AziDesigns/IRLKTANE/IRLKTANE/knob.h

// On the Subject of Knobs
/*
  KNOWN ISSUES:
  MODULE FULLY FUNCTIONS FROM A LED RANDOMAZATION, KNOB TRACKING, AND RESETTING TIME ETC,
    HOWEVER THE UP POSITION HAS STILL NOT BEEN DETERMINED, IN GAME UP IS ROTATED TO BE LEFT RIGHT UP OR DOWN AT RANDOM EACH TIME IT RESETS. 
    MINE IS CURRENTLY GOING TO BE HARD VALUE OF UP = UP AND NO MOVING LABEL. MAY ADD A MOTOR THAT ROTATES THE UP POSITION IN THE FUTURE.
*/
#define KNOB_DEFAULT_TIME 40 // default time per rotation
#define PIN_KNOB_ROTARY_SWITCH A0 // rotary switch analog input pin
#define PIN_KNOB_LED_1  2,1,1
#define PIN_KNOB_LED_2  2,2,1
#define PIN_KNOB_LED_3  2,3,1
#define PIN_KNOB_LED_4  2,4,1
#define PIN_KNOB_LED_5  2,5,1
#define PIN_KNOB_LED_6  2,6,1l
#define PIN_KNOB_LED_7  2,7,1
#define PIN_KNOB_LED_8  2,0,2
#define PIN_KNOB_LED_9  2,1,2
#define PIN_KNOB_LED_10 2,2,2
#define PIN_KNOB_LED_11 2,3,2
#define PIN_KNOB_LED_12 2,4,2
#define KNOB_POSITION_4 200
#define KNOB_POSITION_3 300
#define KNOB_POSITION_2 450
#define KNOB_POSITION_1 1023

unsigned long knobSeconds = 0;
byte knobSec = KNOB_DEFAULT_TIME + 1;

byte knobLEDArray = 0;
int knobPositionValue = 0;
byte knobCurrentState = 0;
byte knobCorrectState = 0;

void knobSetup() 
{
  if (DEBUG_LEVEL >= 3) {
    Serial.println (__func__);
  }
  knobLEDArray = random(8);
};

void knobCheckKnobPosition() // function that checks if the knob is in the correct position when it hits -1
{
  knobPositionValue = analogRead(PIN_KNOB_ROTARY_SWITCH); // uncomment once the knob is wired up. Right now its not wired at all.
  if (knobPositionValue<=KNOB_POSITION_4){
    if (DEBUG_LEVEL >= 1) {
      Serial.println(F("Position 4"));
    }
    knobCurrentState = 4;
  } else if (knobPositionValue<=KNOB_POSITION_3) {
    if (DEBUG_LEVEL >= 1) {
      Serial.println(F("Position 3"));
    }
    knobCurrentState = 3;
  } else if (knobPositionValue<=KNOB_POSITION_2) {
    if (DEBUG_LEVEL >= 1) {
      Serial.println(F("Position 2"));
    }
    knobCurrentState = 2;
  } else if (knobPositionValue<=KNOB_POSITION_1) {
    if (DEBUG_LEVEL >= 1) {
      Serial.println(F("Position 1"));
    }
    knobCurrentState = 1;
  }
}

void knobDisplayTime() // function that displays the time on the clock
{
  if (DEBUG_LEVEL >= 3) {
    Serial.println (__func__);
  }
  if (knobSeconds < millis()) {
    knobSeconds += 1000;
    knobSec--;
    if (knobSec == -1) {
      knobCheckKnobPosition();
      if (knobCurrentState==knobCorrectState) { 
        knobSec=KNOB_DEFAULT_TIME + 1; // command to restart the countdown timer
        knobLEDArray = random(8); // choses a new random array of LED's to display
      } else {
        addStrike(); // if the time hits zero and the correct knob position is not set the bomb will add a stike
        knobModuleStike = true;
        lc.setDigit(1,5,' ',false);
        lc.setDigit(1,4,' ',false); 
        lc.setLed(PIN_KNOB_LED_1,false);
        lc.setLed(PIN_KNOB_LED_2,false);
        lc.setLed(PIN_KNOB_LED_3,false);
        lc.setLed(PIN_KNOB_LED_4,false);
        lc.setLed(PIN_KNOB_LED_5,false);
        lc.setLed(PIN_KNOB_LED_6,false);
        lc.setLed(PIN_KNOB_LED_7,false);
        lc.setLed(PIN_KNOB_LED_8,false);
        lc.setLed(PIN_KNOB_LED_9,false);
        lc.setLed(PIN_KNOB_LED_10,false);
        lc.setLed(PIN_KNOB_LED_11,false);
        lc.setLed(PIN_KNOB_LED_12,false);
      }
    }
    needyDigitDisplay(1, 4, 5, knobSec);
  }
}

void knobDisplayLEDArray()
{
  if (knobLEDArray==0) {
    knobCorrectState=0; // correct position = up
    lc.setLed(PIN_KNOB_LED_1,false);
    lc.setLed(PIN_KNOB_LED_2,false);
    lc.setLed(PIN_KNOB_LED_3,true);
    lc.setLed(PIN_KNOB_LED_4,false);
    lc.setLed(PIN_KNOB_LED_5,true);
    lc.setLed(PIN_KNOB_LED_6,true);
    lc.setLed(PIN_KNOB_LED_7,true);
    lc.setLed(PIN_KNOB_LED_8,true);
    lc.setLed(PIN_KNOB_LED_9,true);
    lc.setLed(PIN_KNOB_LED_10,true);
    lc.setLed(PIN_KNOB_LED_11,false);
    lc.setLed(PIN_KNOB_LED_12,true);
  } else if (knobLEDArray==1) {
    knobCorrectState=0; // correct position = up
    lc.setLed(PIN_KNOB_LED_1,true);
    lc.setLed(PIN_KNOB_LED_2,false);
    lc.setLed(PIN_KNOB_LED_3,true);
    lc.setLed(PIN_KNOB_LED_4,false);
    lc.setLed(PIN_KNOB_LED_5,true);
    lc.setLed(PIN_KNOB_LED_6,false);
    lc.setLed(PIN_KNOB_LED_7,false);
    lc.setLed(PIN_KNOB_LED_8,true);
    lc.setLed(PIN_KNOB_LED_9,true);
    lc.setLed(PIN_KNOB_LED_10,false);
    lc.setLed(PIN_KNOB_LED_11,true);
    lc.setLed(PIN_KNOB_LED_12,true);
  } else if (knobLEDArray==2) {
    knobCorrectState=2; // correct position = down
    lc.setLed(PIN_KNOB_LED_1,false);
    lc.setLed(PIN_KNOB_LED_2,true);
    lc.setLed(PIN_KNOB_LED_3,true);
    lc.setLed(PIN_KNOB_LED_4,false);
    lc.setLed(PIN_KNOB_LED_5,false);
    lc.setLed(PIN_KNOB_LED_6,true);
    lc.setLed(PIN_KNOB_LED_7,true);
    lc.setLed(PIN_KNOB_LED_8,true);
    lc.setLed(PIN_KNOB_LED_9,true);
    lc.setLed(PIN_KNOB_LED_10,true);
    lc.setLed(PIN_KNOB_LED_11,false);
    lc.setLed(PIN_KNOB_LED_12,true);
  } else if (knobLEDArray==3) {
    knobCorrectState=2; // correct position = down
    lc.setLed(PIN_KNOB_LED_1,true);
    lc.setLed(PIN_KNOB_LED_2,false);
    lc.setLed(PIN_KNOB_LED_3,true);
    lc.setLed(PIN_KNOB_LED_4,false);
    lc.setLed(PIN_KNOB_LED_5,true);
    lc.setLed(PIN_KNOB_LED_6,false);
    lc.setLed(PIN_KNOB_LED_7,false);
    lc.setLed(PIN_KNOB_LED_8,true);
    lc.setLed(PIN_KNOB_LED_9,false);
    lc.setLed(PIN_KNOB_LED_10,false);
    lc.setLed(PIN_KNOB_LED_11,false);
    lc.setLed(PIN_KNOB_LED_12,true);
  } else if (knobLEDArray==4) {
    knobCorrectState=3; // correct position = left
    lc.setLed(PIN_KNOB_LED_1,false);
    lc.setLed(PIN_KNOB_LED_2,false);
    lc.setLed(PIN_KNOB_LED_3,false);
    lc.setLed(PIN_KNOB_LED_4,false);
    lc.setLed(PIN_KNOB_LED_5,true);
    lc.setLed(PIN_KNOB_LED_6,false);
    lc.setLed(PIN_KNOB_LED_7,true);
    lc.setLed(PIN_KNOB_LED_8,false);
    lc.setLed(PIN_KNOB_LED_9,false);
    lc.setLed(PIN_KNOB_LED_10,true);
    lc.setLed(PIN_KNOB_LED_11,true);
    lc.setLed(PIN_KNOB_LED_12,true);
  } else if (knobLEDArray==5) {
    knobCorrectState=3; // correct position = left
    lc.setLed(PIN_KNOB_LED_1,false);
    lc.setLed(PIN_KNOB_LED_2,false);
    lc.setLed(PIN_KNOB_LED_3,false);
    lc.setLed(PIN_KNOB_LED_4,false);
    lc.setLed(PIN_KNOB_LED_5,true);
    lc.setLed(PIN_KNOB_LED_6,false);
    lc.setLed(PIN_KNOB_LED_7,false);
    lc.setLed(PIN_KNOB_LED_8,false);
    lc.setLed(PIN_KNOB_LED_9,false);
    lc.setLed(PIN_KNOB_LED_10,true);
    lc.setLed(PIN_KNOB_LED_11,true);
    lc.setLed(PIN_KNOB_LED_12,false);
  } else if (knobLEDArray==6) {
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
  lc.setLed(PIN_KNOB_LED_5,false);
  lc.setLed(PIN_KNOB_LED_6,false);
  lc.setLed(PIN_KNOB_LED_7,false);
  lc.setLed(PIN_KNOB_LED_8,false);
  lc.setLed(PIN_KNOB_LED_9,false);
  lc.setLed(PIN_KNOB_LED_10,false);
  lc.setLed(PIN_KNOB_LED_11,false);
  lc.setLed(PIN_KNOB_LED_12,false);
}
