AziDesigns/IRLKTANE/IRLKTANE/batteries.h

/*************************************************
   Default values for batteries
 *************************************************/
/*
  KNOWN ISSUES:
  Will eventually become a random number of batteries and actualy display them. For now it is fixed values
*/
byte nrBatteries = 0; // number of batteries // will eventually point to a .h file that controls which batteries are shown
