AziDesigns/IRLKTANE/IRLKTANE/indicator.h

/*************************************************
   Default values for indicators
 *************************************************/
/*
  KNOWN ISSUES:
  Will eventually become a random selection of indicatiors displayed and random 50/50 if they are lit or not. 
  For now it is fixed values
*/
bool indicatorCAR = false;
bool indicatorCARLit = false;
bool indicatorFRK = false;
bool indicatorFRKLit = false;
